Archive-663/seagull_4a_TLR/ASSETS/PHOTO/PRODUCT/2 (3).jpg

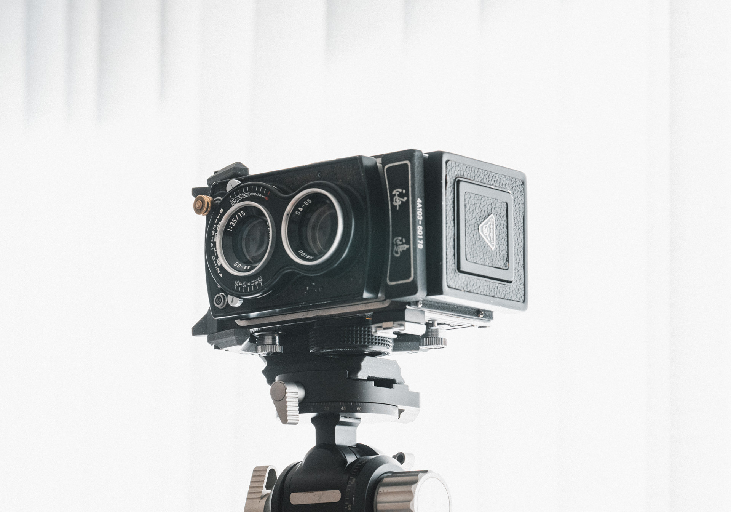
ASSETS/PHOTO/PRODUCT/2 (3).jpg
