Archive-663/seagull_4a_TLR/ASSETS/PHOTO/PRODUCT/2 (5).jpg

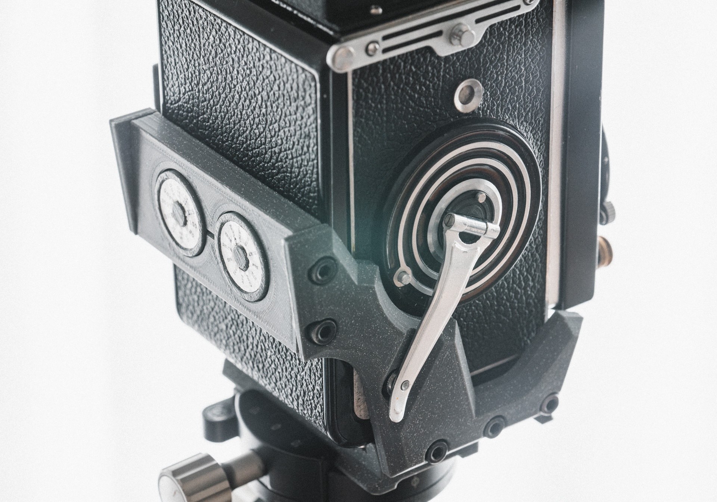
ASSETS/PHOTO/PRODUCT/2 (5).jpg
