Archive-663/seagull_4a_TLR/ASSETS/PHOTO/SAMPLE/1 (1).jpg

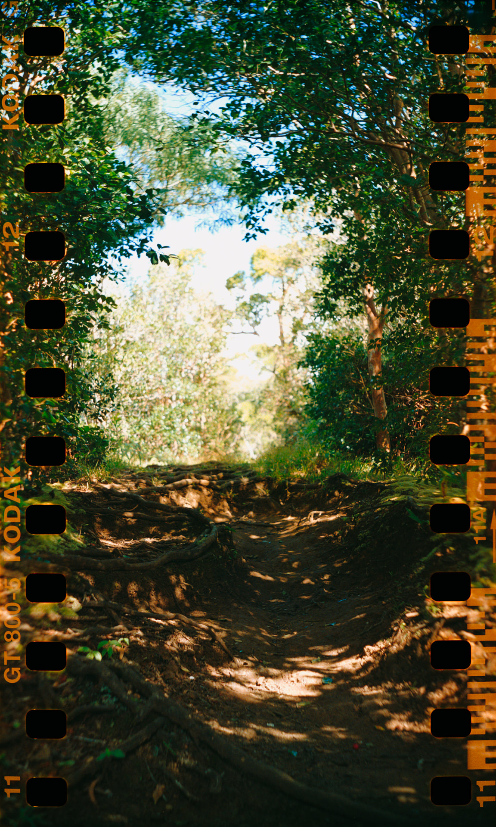
ASSETS/PHOTO/SAMPLE/1 (1).jpg
