Archive-663/seagull_4a_TLR/ASSETS/PHOTO/SAMPLE/1 (4).jpg

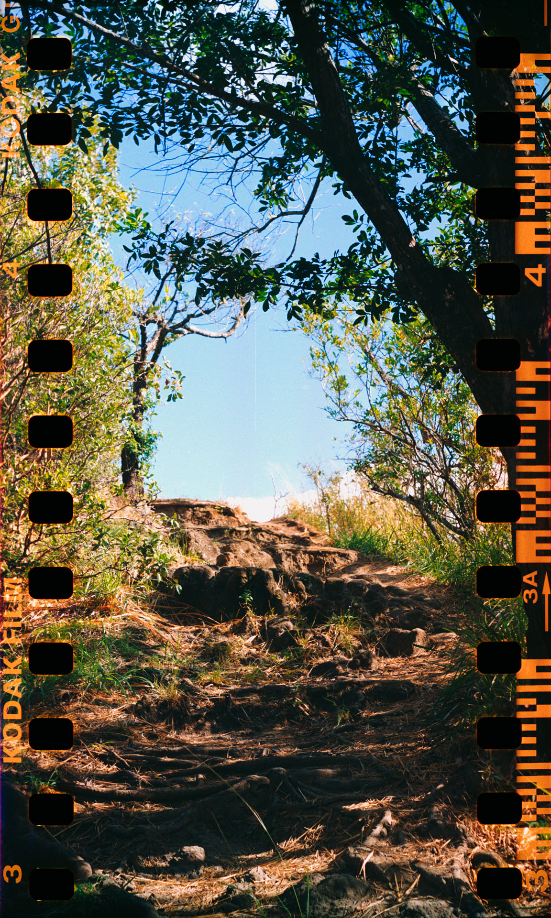
ASSETS/PHOTO/SAMPLE/1 (4).jpg
