Archive-663/seagull_4a_TLR/Jawbone Half Cage/STEP/seagull4A_l-Bracket_arcaSwissBase_002.stp

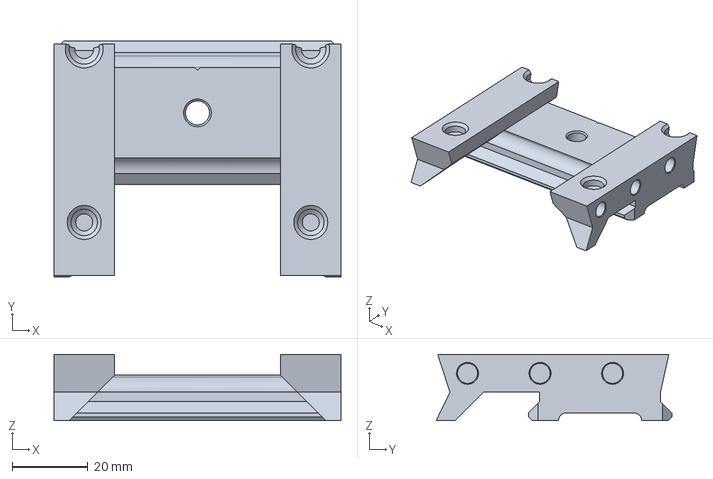
[picture p26: CAD file, 2026-01-14]
Jawbone Half Cage/STEP/seagull4A_l-Bracket_arcaSwissBase_002.stp
76.0 x 62.4 x 17.5 mm
